SadaleNet/ilo-nena/cardboard_label/cardboard_label.jpg

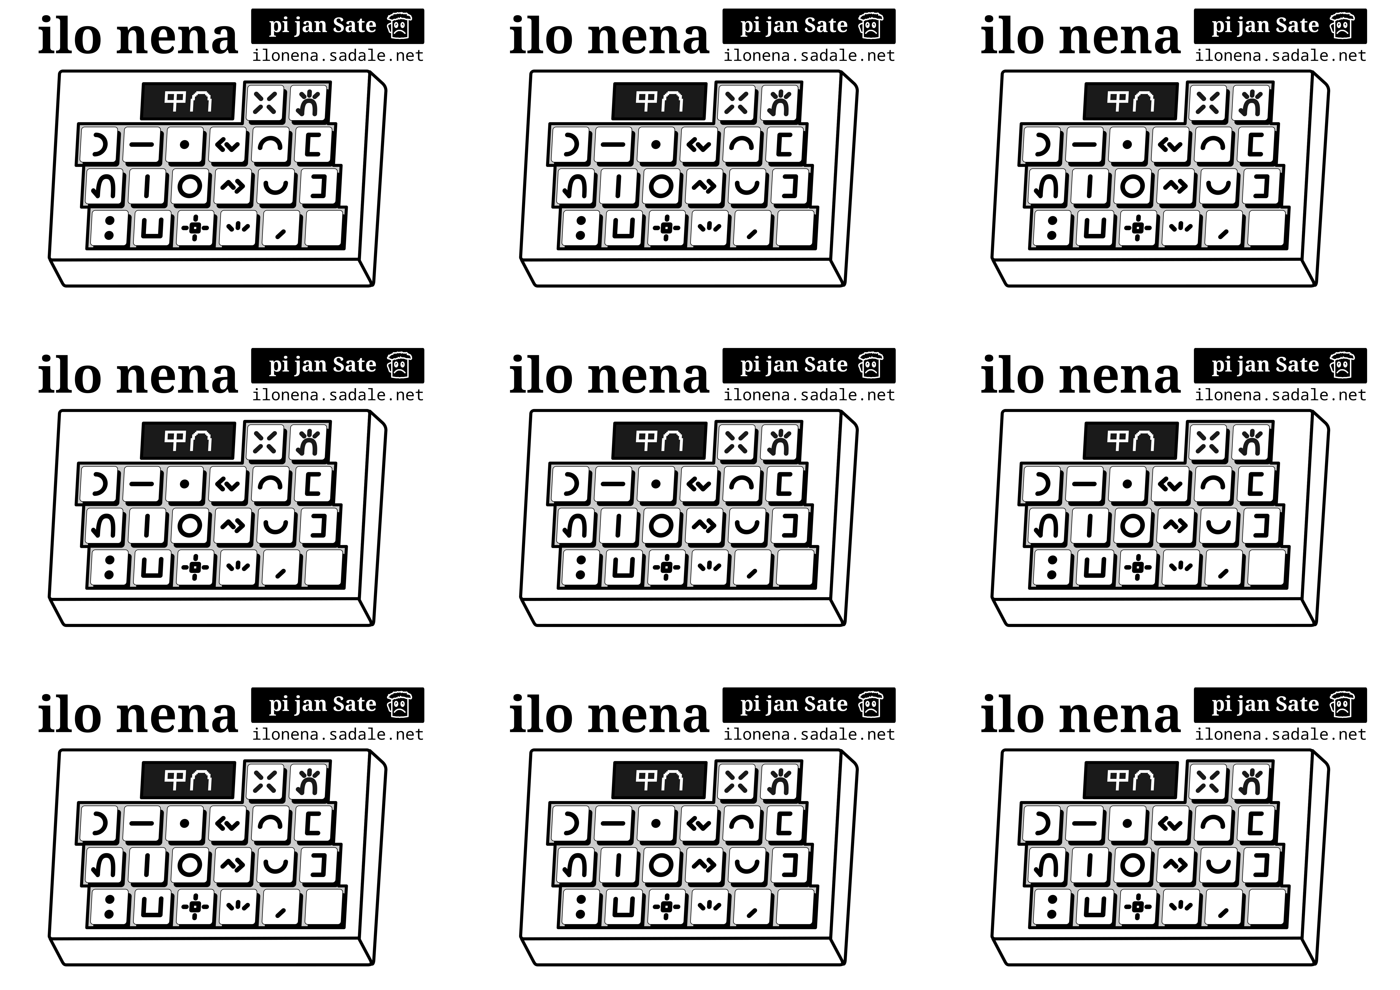
cardboard_label/cardboard_label.jpg
