SadaleNet/ilo-nena/keycap_label/ilonena-label.png

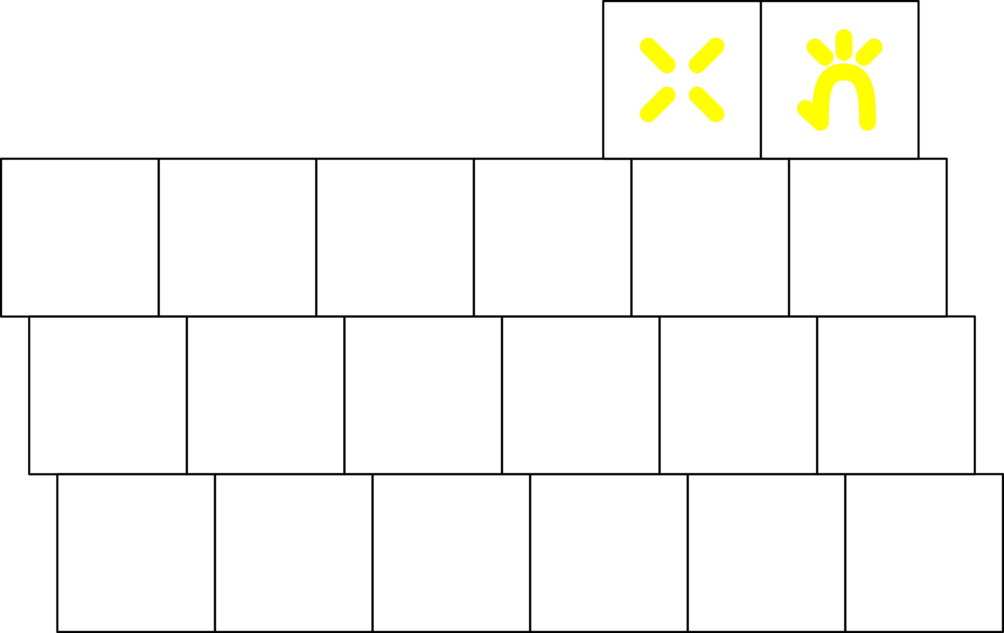
keycap_label/ilonena-label.png
