SadaleNet/ilo-nena/src/lookup.c

// Copyright 2025 Wong Cho Ching <https://sadale.net>
//
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
// 1. Redistributions of source code must retain the above copyright
// notice, this list of conditions and the following disclaimer.
//
// 2. Redistributions in binary form must reproduce the above copyright
// notice, this list of conditions and the following disclaimer in the
// documentation and/or other materials provided with the distribution.
//
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
#include "lookup.h"
#include "keyboard.h"
#include <string.h>
#include <stdlib.h>
#include <stdint.h>

const uint32_t LOOKUP_CODEPAGE_3_START = 0xFFFF2000U;
const size_t LOOKUP_CODEPAGE_3_LENGTH = INTERNAL_IMAGE_NUM;

uint64_t encode_input_buffer_as_u52(uint8_t input_buffer[12], size_t input_buffer_length) {
	uint64_t ret_u52 = 0;
	if(input_buffer_length > 12) {
		// Input sequence too long. Returning 0
		return 0;
	}

	// Determine if complex mode is required
	for(size_t i=0; i<input_buffer_length; i++) {
		if(input_buffer[i] == ILONENA_KEY_A || input_buffer[i] >= ILONENA_KEY_G) {
			ret_u52 |= LOOKUP_FULL_ENTRY_COMPLEX_MODE;
			if(input_buffer_length > 10) {
				// Input sequence too long for complex mode. Returning 0
				return 0;
			}
			break;
		}
	}

	if(ret_u52 & LOOKUP_FULL_ENTRY_COMPLEX_MODE) {
		// Complex mode encoding
		uint64_t shift = 50-5;
		for(size_t i=0; i<input_buffer_length; i++) {
			ret_u52 |= (uint64_t)input_buffer[i] << shift;
			shift -= 5;
		}
	} else {
		// Simple mode encoding
		uint64_t shift = 48-4;
		for(size_t i=0; i<input_buffer_length; i++) {
			uint32_t key_id = input_buffer[i];
			if(key_id > ILONENA_KEY_A) {
				key_id--;
			}
			ret_u52 |= (uint64_t)key_id << shift;
			shift -= 4;
		}
	}

	return ret_u52;
}

static uint32_t encode_input_buffer_as_u24(uint8_t input_buffer[6], size_t input_buffer_length) {
	if(input_buffer_length > 6) {
		// Invalid input. Returning 0.
		return 0;
	}

	uint32_t ret = 0;
	uint64_t shift = 24-4;

	for(size_t i=0; i<input_buffer_length; i++) {
		uint32_t key_id = input_buffer[i];
		if(key_id == ILONENA_KEY_A || key_id >= ILONENA_KEY_G) {
			// Invalid input. Returning 0.
			return 0;
		} else if(key_id > ILONENA_KEY_A) {
			key_id--;
		}
		ret |= key_id << shift;
		shift -= 4;
	}
	return ret;
}

uint32_t lookup_search(uint8_t input_buffer[12], size_t input_buffer_length) {
	if(input_buffer_length <= 0 || input_buffer_length > 12) {
		return 0;
	}

	uint32_t ret = 0;
	uint32_t target = encode_input_buffer_as_u24(input_buffer, input_buffer_length);
	// Only check COMPACT_TABLE if the input criteria has been met (such that encode_input_buffer_as_u24() returns a valid value)
	if(target != 0) {
		for(size_t i=0; i<LOOKUP_COMPACT_TABLE_LENGTH; i++) {
			if(target == LOOKUP_COMPACT_TABLE[i].input) {
				ret = LOOKUP_CODEPAGE_0_START + LOOKUP_COMPACT_TABLE[i].sitelen_pona_id;
			}
		}
	}

	// Couldn't find the entry in LOOKUP_COMPACT_TABLE. Let's check the other more complicated table
	if(!ret) {
		uint64_t target = encode_input_buffer_as_u52(input_buffer, input_buffer_length);
		for(size_t i=0; i<LOOKUP_FULL_TABLE_LENGTH; i++) {
			if(target == LOOKUP_FULL_TABLE[i].input_u52) {
				switch(LOOKUP_FULL_TABLE[i].codepage) {
					case 0:
						ret = LOOKUP_CODEPAGE_0_START + LOOKUP_FULL_TABLE[i].code_id;
					break;
					case 1:
						ret = LOOKUP_CODEPAGE_1_START + LOOKUP_FULL_TABLE[i].code_id;
					break;
					case 2:
						ret = LOOKUP_CODEPAGE_2_START + LOOKUP_FULL_TABLE[i].code_id;
					break;
					case 3:
						ret = 0; // Reserved for future use
					break;
				}
			}
		}
	}
	return ret;
}

const char* lookup_get_ascii_string(uint8_t codepage, size_t index) {
	const char *ret = NULL;
	switch(codepage) {
		case 0:
			ret = LOOKUP_CODEPAGE_0;
		break;
		case 1:
			ret = LOOKUP_CODEPAGE_1;
		break;
		default:
			return NULL;
	}

	// Scroll past #index amount of NULL terminators, then return the string
	while(index--) {
		while(*ret++);
	}
	return ret;
}

const uint32_t* lookup_get_unicode_string(uint8_t codepage, size_t index) {
	if(codepage == 2) {
		return LOOKUP_CODEPAGE_2[index];
	}
	return NULL;
}

static uint8_t lookup_get_nibble(const uint8_t *array, size_t index) {
	if(index%2 == 1) {
		return (array[index/2] >>4 ) & 0x0F;
	}
	return array[index/2] & 0x0F;
}

static void lookup_decompress_image(uint16_t image[LOOKUP_IMAGE_WIDTH], const uint8_t *compressed_data) {
	size_t payload_length = (compressed_data[0] & 0x1F)*2; // Unit: nibbles
	size_t start_col = (compressed_data[0] & 0xE0) >> 5;
	size_t current_col = start_col;
	size_t end_col = LOOKUP_IMAGE_WIDTH-start_col; // Exclusive!

	if(payload_length == 0) {
		memset(image, 0, sizeof(*image)*LOOKUP_IMAGE_WIDTH);
		return;
	}

	// Fill the image with black bars on the sides (i.e. cropping handling)
	for(size_t i=0; i<start_col; i++) {
		image[i] = 0x00;
		image[LOOKUP_IMAGE_WIDTH-1-i] = 0x00;
	}

	static uint16_t dictionary[8];
	size_t dictionary_index = 0;
	size_t i=0;
	while(i < payload_length && current_col < end_col) {
		if(lookup_get_nibble(&compressed_data[1], i) & 0x01) {
			// Dictionary-mapped column
			image[current_col++] = dictionary[lookup_get_nibble(&compressed_data[1], i++) >> 1];
		} else if(i+1 < payload_length) {
			// Non-dictionary mapped column
			image[current_col] = lookup_get_nibble(&compressed_data[1], i++);
			image[current_col] |= lookup_get_nibble(&compressed_data[1], i++) << 4;
			image[current_col] |= lookup_get_nibble(&compressed_data[1], i++) << 8;
			image[current_col] |= lookup_get_nibble(&compressed_data[1], i++) << 12;
			image[current_col] >>= 1;
			dictionary[dictionary_index++%8] = image[current_col++];
		} else {
			// Final padding nibble for aligning to 8 bytes. Ignore!
			break;
		}
	}

	if(current_col == 8) {
		// Symmetric image. Only half of the image is encoded in the data
		// Let's draw the second half that's mirrored with the first half
		for(; current_col<end_col; current_col++) {
			image[current_col] = image[LOOKUP_IMAGE_WIDTH-1-current_col];
		}
	}
}

static const uint8_t* lookup_get_image_ptr_by_index(const uint8_t *data_array, size_t index) {
	const uint8_t *ret = data_array;
	while(index--) {
		ret += (ret[0] & 0x1F) + 1;
	}
	return ret;
}

void lookup_get_image(uint16_t image[LOOKUP_IMAGE_WIDTH], uint32_t codepoint) {
	const uint8_t *font_data_ptr;
	if(codepoint >= LOOKUP_CODEPAGE_0_START && codepoint < LOOKUP_CODEPAGE_0_START+LOOKUP_CODEPAGE_0_LENGTH) {
		font_data_ptr = lookup_get_image_ptr_by_index(FONT_CODEPAGE_0, codepoint-LOOKUP_CODEPAGE_0_START);
	} else if(codepoint >= LOOKUP_CODEPAGE_1_START && codepoint < LOOKUP_CODEPAGE_1_START+LOOKUP_CODEPAGE_1_LENGTH) {
		font_data_ptr = lookup_get_image_ptr_by_index(FONT_CODEPAGE_1, codepoint-LOOKUP_CODEPAGE_1_START);
	} else if(codepoint >= LOOKUP_CODEPAGE_2_START && codepoint < LOOKUP_CODEPAGE_2_START+LOOKUP_CODEPAGE_2_LENGTH) {
		font_data_ptr = lookup_get_image_ptr_by_index(FONT_CODEPAGE_2, codepoint-LOOKUP_CODEPAGE_2_START);
	} else if(codepoint >= LOOKUP_CODEPAGE_3_START && codepoint < LOOKUP_CODEPAGE_3_START+LOOKUP_CODEPAGE_3_LENGTH) {
		font_data_ptr = lookup_get_image_ptr_by_index(FONT_CODEPAGE_3, codepoint-LOOKUP_CODEPAGE_3_START);
	} else {
		memset(image, 0, 15*2);
		return;
	}
	lookup_decompress_image(image, font_data_ptr);
}
