SadaleNet/ilo-nena/src/lookup.h

// Copyright 2025 Wong Cho Ching <https://sadale.net>
//
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
// 1. Redistributions of source code must retain the above copyright
// notice, this list of conditions and the following disclaimer.
//
// 2. Redistributions in binary form must reproduce the above copyright
// notice, this list of conditions and the following disclaimer in the
// documentation and/or other materials provided with the distribution.
//
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
#ifndef ILONENA_LOOKUP_H
#define ILONENA_LOOKUP_H

#include <stdint.h>
#include <stdlib.h> // For size_t

#define LOOKUP_INPUT_LENGTH_MAX (12)

enum ilonena_key_id {
	ILONENA_KEY_NONE,
	ILONENA_KEY_1,
	ILONENA_KEY_2,
	ILONENA_KEY_3,
	ILONENA_KEY_4,
	ILONENA_KEY_5,
	ILONENA_KEY_6,
	ILONENA_KEY_Q,
	ILONENA_KEY_W,
	ILONENA_KEY_E,
	ILONENA_KEY_R,
	ILONENA_KEY_T,
	ILONENA_KEY_Y,
	ILONENA_KEY_A, // colon - skipped in lookup_compact_entry
	ILONENA_KEY_S,
	ILONENA_KEY_D,
	ILONENA_KEY_F,
	ILONENA_KEY_G, // comma - skipped in lookup_compact_entry
	ILONENA_KEY_ALA,
	ILONENA_KEY_WEKA,
	ILONENA_KEY_PANA,
};

#define LOOKUP_IMAGE_WIDTH (15U)

// Images that couldn't be typed out
enum internal_image {
	INTERNAL_IMAGE_1,
	INTERNAL_IMAGE_2,
	INTERNAL_IMAGE_3,
	INTERNAL_IMAGE_4,
	INTERNAL_IMAGE_5,
	INTERNAL_IMAGE_6,
	INTERNAL_IMAGE_Q,
	INTERNAL_IMAGE_W,
	INTERNAL_IMAGE_E,
	INTERNAL_IMAGE_R,
	INTERNAL_IMAGE_T,
	INTERNAL_IMAGE_Y,
	INTERNAL_IMAGE_A,
	INTERNAL_IMAGE_S,
	INTERNAL_IMAGE_D,
	INTERNAL_IMAGE_F,
	INTERNAL_IMAGE_G,
	INTERNAL_IMAGE_LATIN,
	INTERNAL_IMAGE_WINDOWS,
	INTERNAL_IMAGE_LINUX,
	INTERNAL_IMAGE_MAC,
	INTERNAL_IMAGE_PUNCTUATION_LATIN_PART1,
	INTERNAL_IMAGE_PUNCTUATION_LATIN_PART2,
	INTERNAL_IMAGE_PUNCTUATION_SITELEN_PONA_PART1,
	INTERNAL_IMAGE_PUNCTUATION_SITELEN_PONA_PART2,
	INTERNAL_IMAGE_PUNCTUATION_LATIN_TRAILING_SPACE_PART1,
	INTERNAL_IMAGE_PUNCTUATION_LATIN_TRAILING_SPACE_PART2,
	INTERNAL_IMAGE_NUM,
};

// Compact entry: stores up to 6 input sequence (cannot store colon nor comma in input sequence), can only output a 8-bit sitelen pona id
struct __attribute__((__packed__)) lookup_compact_entry {
	uint32_t input:24; // each key takes 4 bits. Cannot encode colon nor comma.
	uint8_t sitelen_pona_id; // ID starting from KEYBOARD_SITELEN_PONA_CODEPOINT_START
};

#define LOOKUP_FULL_ENTRY_COMPLEX_MODE ((uint64_t)1ULL<<51) // Complex mode allows encoding colon and comma, at the cost of shorter input limit

// Full entry: stores either up to 12 input sequence (w/o colon nor comma) or 10 input sequence (w/ colon or comma), can output id of 3 different pages.
// To output a string, use virtual codepoints
struct __attribute__((__packed__)) lookup_full_entry {
	uint64_t input_u52:52; // Stores either a) 12 input sequence without colon nor comma or b) 10 input sequence with colon or comma.
	uint8_t codepage:2; // 0 - sitelen pona table. 1 - ASCII string table. 2 - Unicode string table. 3 - reserved
	uint8_t padding:2; // reserved
	uint8_t code_id;
};

uint32_t lookup_search(uint8_t input_buffer[LOOKUP_INPUT_LENGTH_MAX], size_t input_buffer_length);
const char* lookup_get_ascii_string(uint8_t codepage, size_t index);
const uint32_t* lookup_get_unicode_string(uint8_t codepage, size_t index);
 void lookup_get_image(uint16_t image[LOOKUP_IMAGE_WIDTH], uint32_t codepoint);

// All of the variables below this point are defined in generated.c
extern const uint32_t LOOKUP_CODEPAGE_0_START;
extern const size_t LOOKUP_CODEPAGE_0_LENGTH;
extern const uint32_t LOOKUP_CODEPAGE_1_START;
extern const size_t LOOKUP_CODEPAGE_1_LENGTH;
extern const uint32_t LOOKUP_CODEPAGE_2_START;
extern const size_t LOOKUP_CODEPAGE_2_LENGTH;
extern const uint32_t LOOKUP_CODEPAGE_3_START;
extern const size_t LOOKUP_CODEPAGE_3_LENGTH;
extern const char *LOOKUP_CODEPAGE_0;
extern const char *LOOKUP_CODEPAGE_1;
extern const uint32_t *LOOKUP_CODEPAGE_2[];

extern const struct lookup_compact_entry LOOKUP_COMPACT_TABLE[];
extern const size_t LOOKUP_COMPACT_TABLE_LENGTH;
extern const struct lookup_full_entry LOOKUP_FULL_TABLE[];
extern const size_t LOOKUP_FULL_TABLE_LENGTH;

extern const uint8_t FONT_CODEPAGE_0[];
extern const uint8_t FONT_CODEPAGE_1[];
extern const uint8_t FONT_CODEPAGE_2[];
extern const uint8_t FONT_CODEPAGE_3[];

#endif
