SadaleNet/ilo-nena/src/funconfig.h

// Taken from rv003usb's example
// https://github.com/cnlohr/rv003usb/blob/f637624a/demo_pikokey_hid/funconfig.h
// The repo of the source file that I took it from is under MIT License

#ifndef _FUNCONFIG_H
#define _FUNCONFIG_H

#define FUNCONF_USE_DEBUGPRINTF 1
#define CH32V003                1
#define FUNCONF_SYSTICK_USE_HCLK 1

#endif
